patrickcollins12/esphome-fan-controller/images/12v fan controller.png

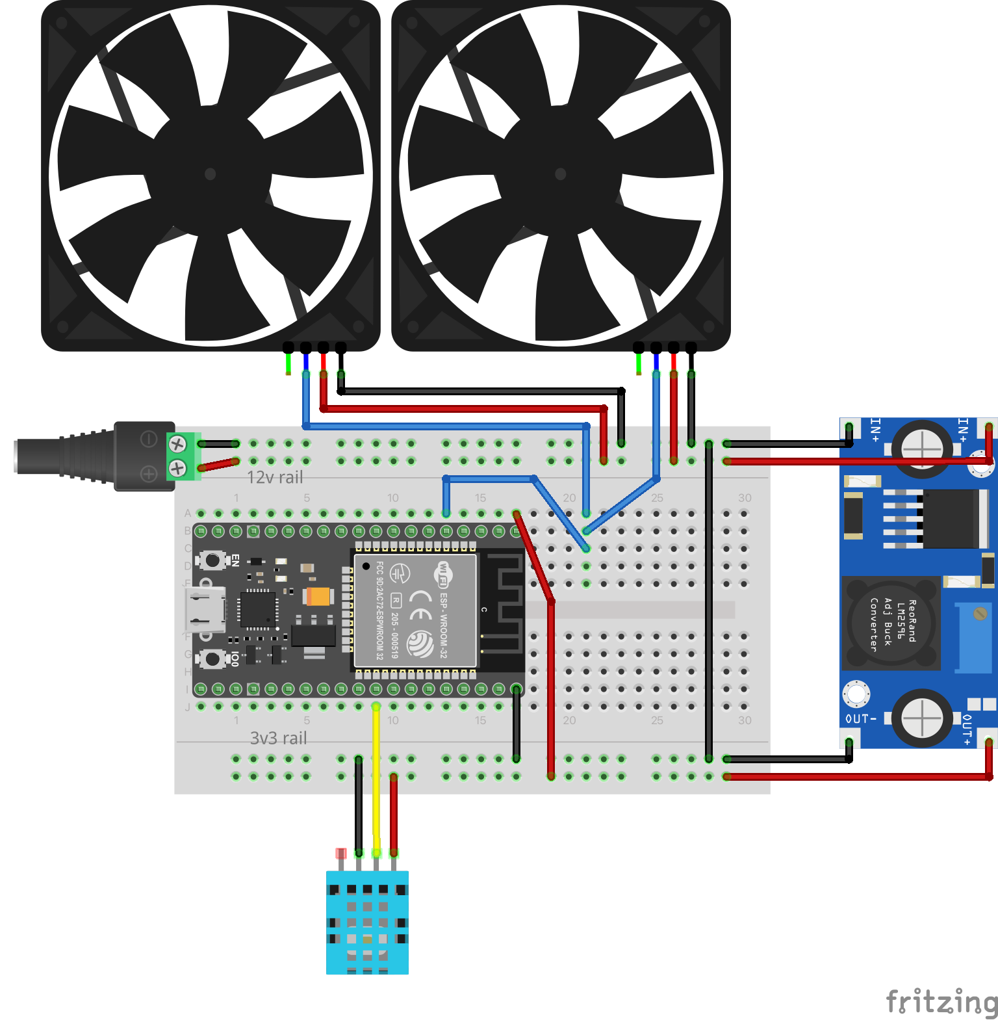
images/12v fan controller.png
